frohlfing/biodom-min/test/test_SensorDS18B20.cpp

/**
 * Unit-Test für die SensorDS18B20-Bibliothek
 */

#include <Arduino.h>
#include <unity.h>
#include "SensorDS18B20.h"

SensorDS18B20 sensor(4); // GPIO4 für 1-Wire

void test_sensor_found() {
    TEST_ASSERT_NOT_EQUAL(1, sensor.getLastError()); // Sensor sollte gefunden sein
}

void test_temperature_valid() {
    TEST_ASSERT_TRUE(sensor.read());
    float temp = sensor.getTemperature();
    TEST_ASSERT_FALSE(isnan(temp));
    TEST_ASSERT(temp > -55.0 && temp < 125.0); // SensorDS18B20 Messbereich
}

void setup() {
    delay(2000); // Sensor-Stabilisierung
    UNITY_BEGIN();
    RUN_TEST(test_sensor_found);
    RUN_TEST(test_temperature_valid);
    UNITY_END();
}

void loop() {}
