frohlfing/biodom-min/test/test_OTA.cpp

/**
 * Unit-Test für die OTA-Bibliothek
 * 
 * Hinweis: Ein echter Unit-Test des OTA-Upload-Prozesses ist nicht möglich,
 * da dies eine Netzwerkverbindung und eine externe Aktion erfordert.
 * Dieser Test prüft lediglich, ob die Klasse instanziiert und ihre
 * Methoden ohne Fehler aufgerufen werden können (Smoke-Test).
 */

#include <Arduino.h>
#include <unity.h>
#include "OTA.h"

// Für den Test wird eine WLAN-Verbindung simuliert.
// In einer echten Testumgebung müsste hier ein WLAN-Mock oder eine
// echte Verbindung aufgebaut werden.
void connect_to_wifi_mock() {
    // In diesem Test wird keine echte Verbindung benötigt, da ArduinoOTA.begin()
    // nicht fehlschlägt, wenn kein WLAN vorhanden ist.
}

void test_ota_initialization() {
    OTA ota("test-host", "test-pass");
    // Rufe begin() auf. In einer echten Umgebung muss WLAN verbunden sein.
    ota.begin();
    TEST_MESSAGE("OTA.begin() wurde aufgerufen.");
}

void test_ota_handle() {
    OTA ota("test-host", "test-pass");
    // Rufe handle() auf. Dies sollte niemals blockieren oder einen Fehler werfen.
    ota.handle();
    TEST_MESSAGE("OTA.handle() wurde aufgerufen.");
}

void setup() {
    delay(2000);
    UNITY_BEGIN();

    connect_to_wifi_mock();
    
    RUN_TEST(test_ota_initialization);
    RUN_TEST(test_ota_handle);

    UNITY_END();
}

void loop() {}
